Hyper-works/Essence/IMG_20220821_130836.jpg

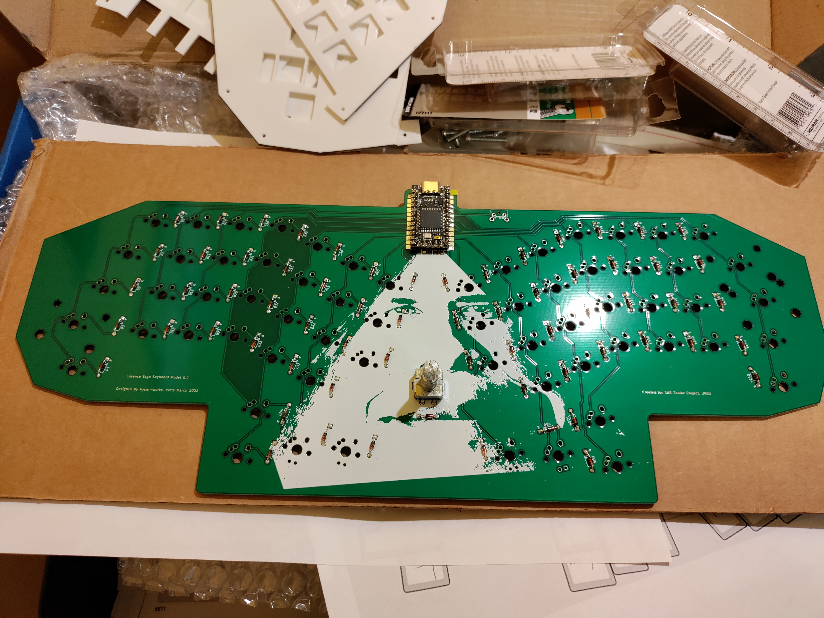
IMG_20220821_130836.jpg
