Hyper-works/Essence/IMG_20220821_130938.jpg

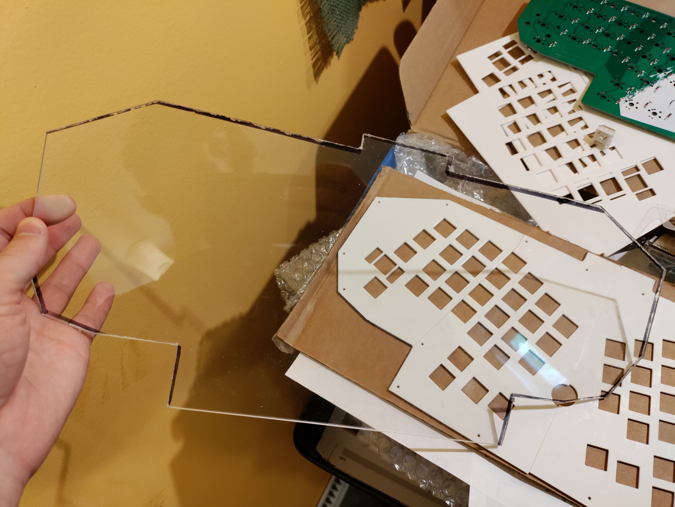
IMG_20220821_130938.jpg
