Hyper-works/Essence/IMG_20220821_130945.jpg

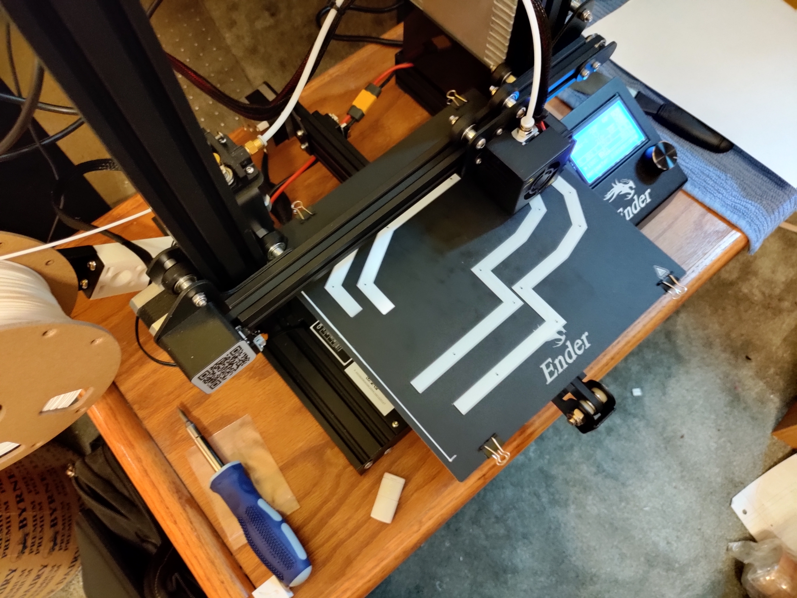
IMG_20220821_130945.jpg
